porcinus/Freeplay-Custom-Addon-Board/preview/01.jpg

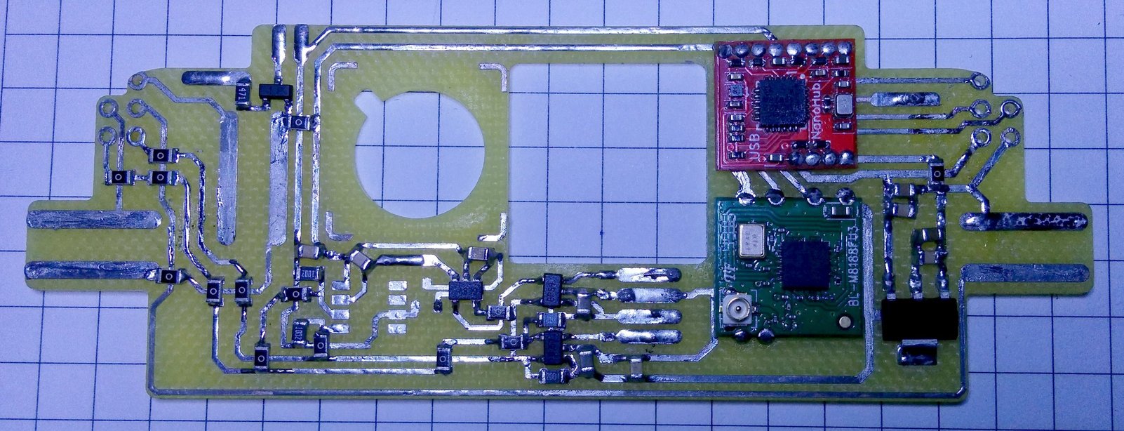
preview/01.jpg
