porcinus/Freeplay-Custom-Addon-Board/preview/03.jpg

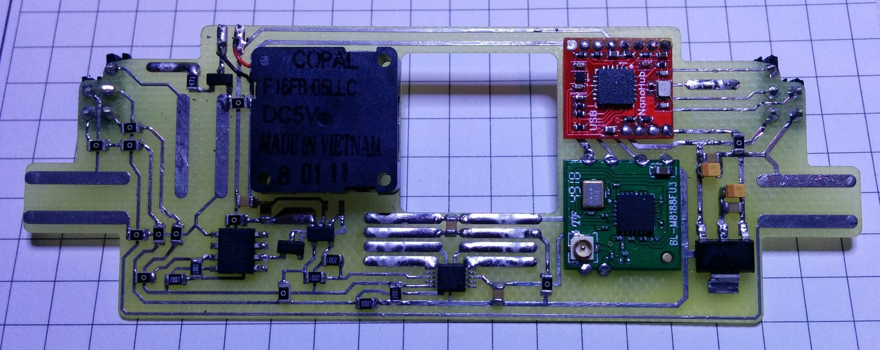
preview/03.jpg
